max3-2/hedgehog-kb/fabrication/centers_fab.dxf

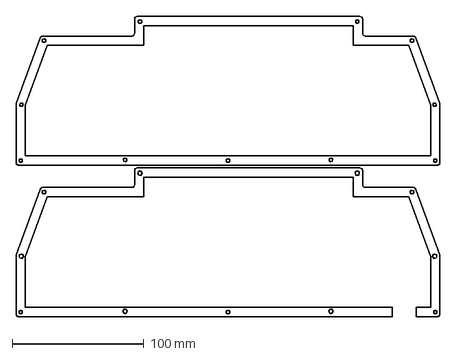
[picture p35: CAD file, 2022-10-11]
fabrication/centers_fab.dxf
321.7 x 228.0 mm
